CarloUser/Mobile-Mapping-Backpack/opencv/calib_images/img_0.png

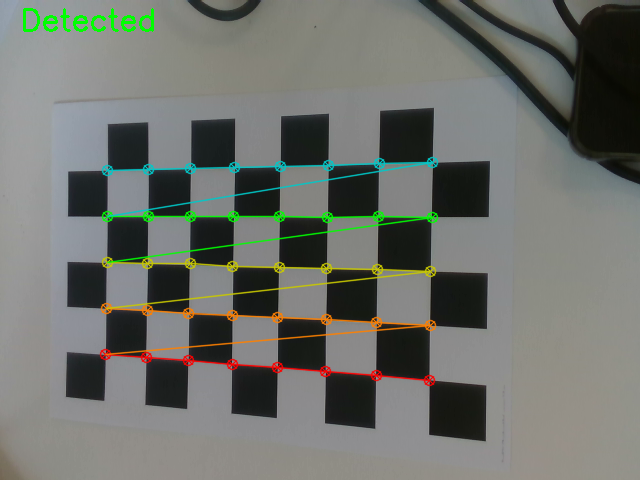
opencv/calib_images/img_0.png
