CarloUser/Mobile-Mapping-Backpack/opencv/calib_images/img_1.png

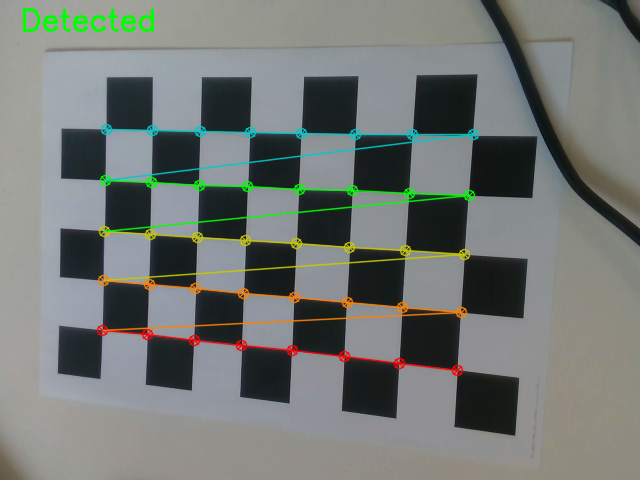
opencv/calib_images/img_1.png
