CarloUser/Mobile-Mapping-Backpack/opencv/calib_images/img_2.png

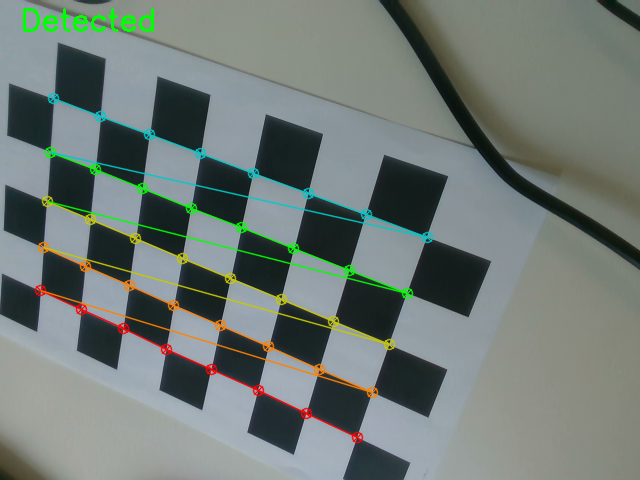
opencv/calib_images/img_2.png
