CarloUser/Mobile-Mapping-Backpack/opencv/calib_images/img_3.png

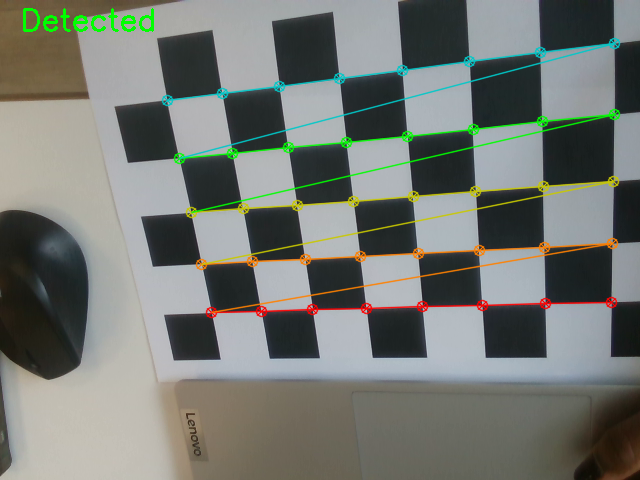
opencv/calib_images/img_3.png
