CarloUser/Mobile-Mapping-Backpack/opencv/calib_images/img_4.png

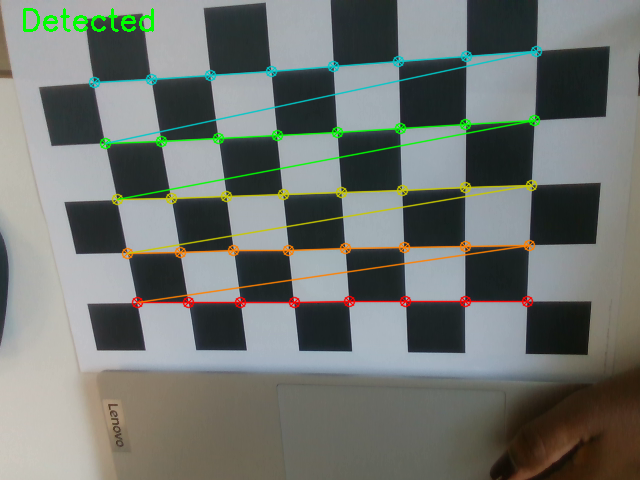
opencv/calib_images/img_4.png
