CarloUser/Mobile-Mapping-Backpack/opencv/calib_images/img_5.png

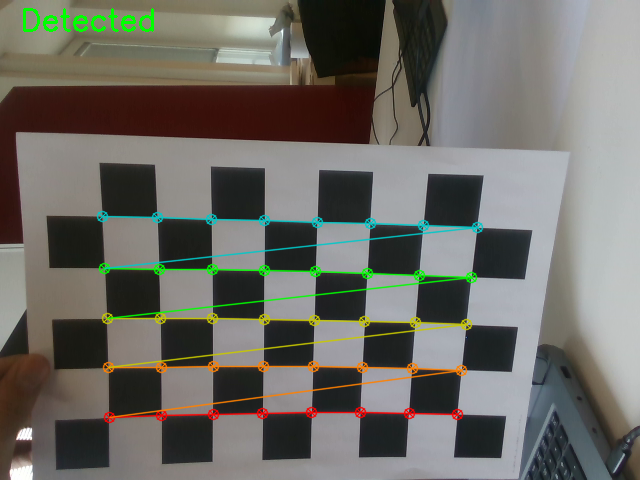
opencv/calib_images/img_5.png
