CarloUser/Mobile-Mapping-Backpack/opencv/calib_images/img_6.png

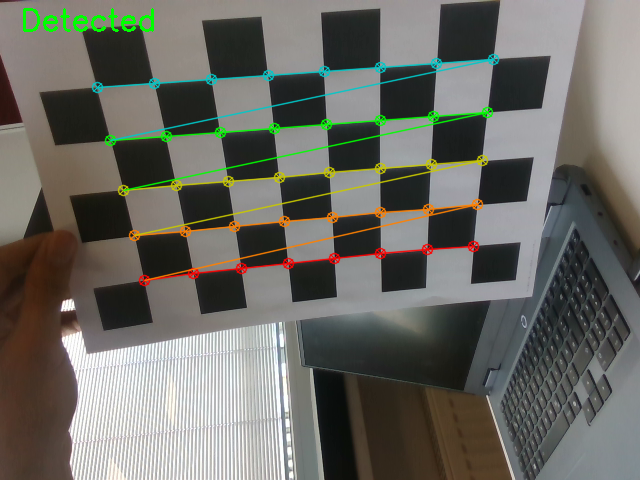
opencv/calib_images/img_6.png
