CarloUser/Mobile-Mapping-Backpack/opencv/calib_images/img_7.png

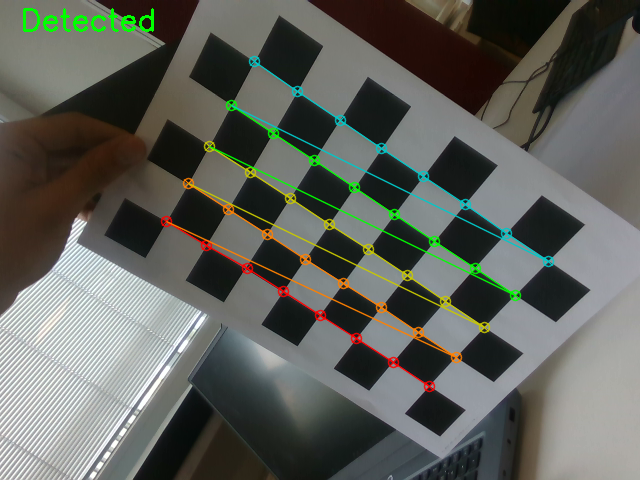
opencv/calib_images/img_7.png
