CarloUser/Mobile-Mapping-Backpack/opencv/calib_images/img_8.png

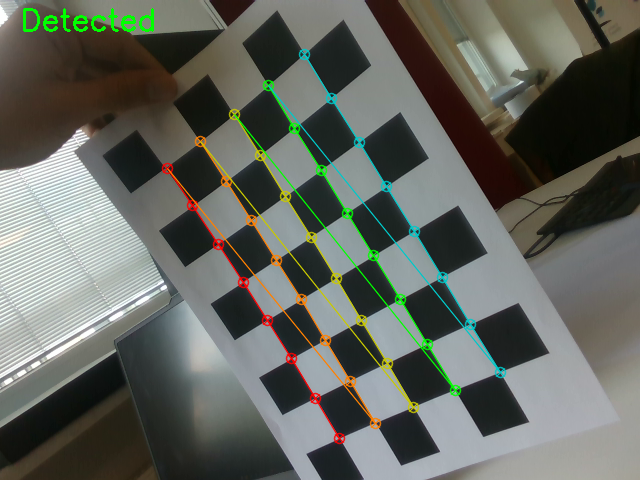
opencv/calib_images/img_8.png
