CarloUser/Mobile-Mapping-Backpack/opencv/calib_images/img_9.png

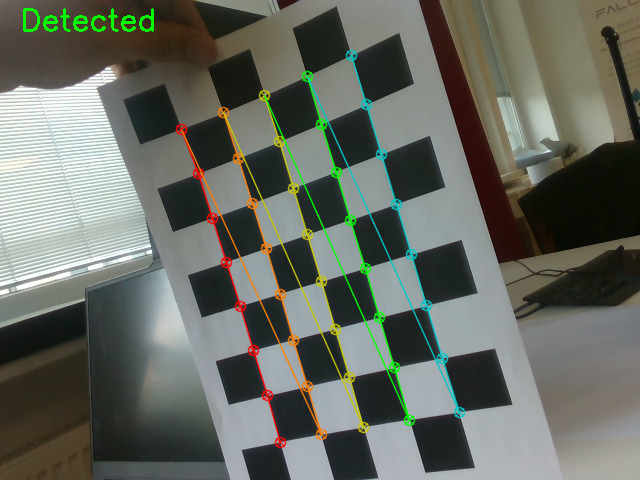
opencv/calib_images/img_9.png
