CarloUser/Mobile-Mapping-Backpack/opencv/calib_images/img_10.png

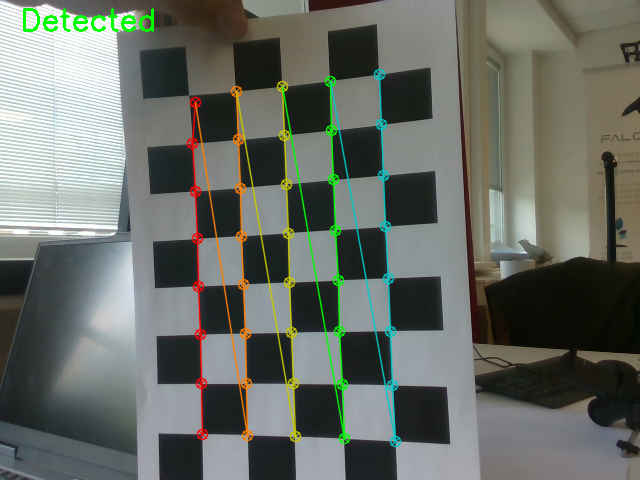
opencv/calib_images/img_10.png
