CarloUser/Mobile-Mapping-Backpack/opencv/calib_images/img_11.png

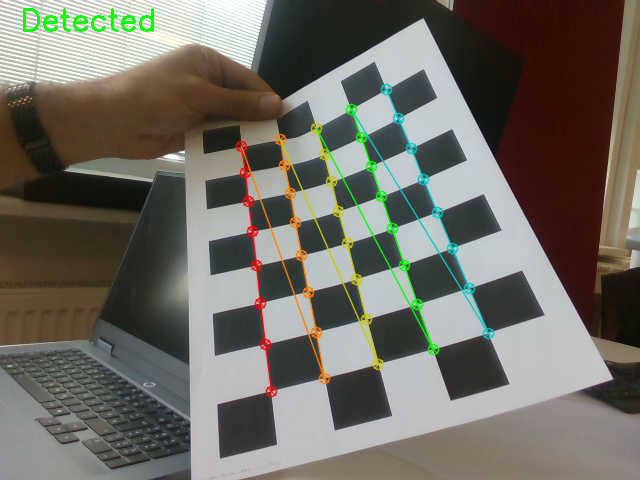
opencv/calib_images/img_11.png
