CarloUser/Mobile-Mapping-Backpack/opencv/calib_images/img_12.png

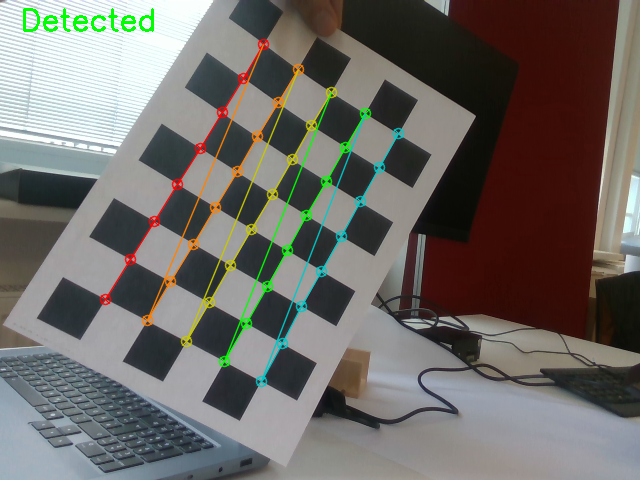
opencv/calib_images/img_12.png
