CarloUser/Mobile-Mapping-Backpack/opencv/calib_images/img_13.png

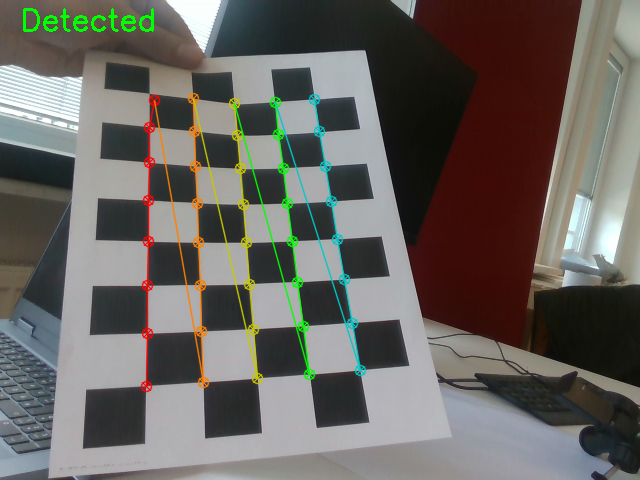
opencv/calib_images/img_13.png
