CarloUser/Mobile-Mapping-Backpack/opencv/calib_images/img_14.png

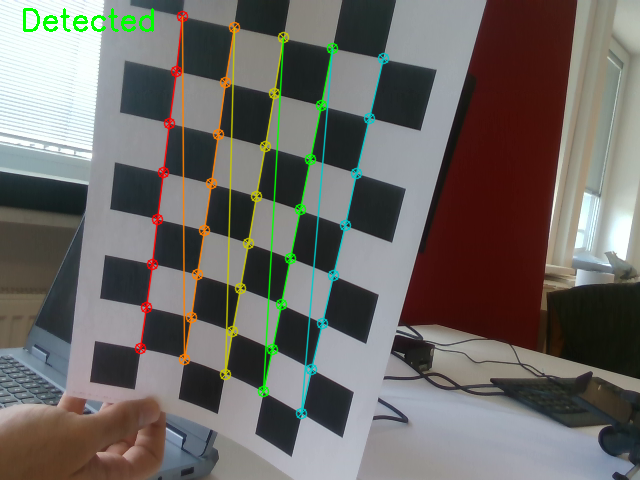
opencv/calib_images/img_14.png
