CarloUser/Mobile-Mapping-Backpack/opencv/calib_images/img_15.png

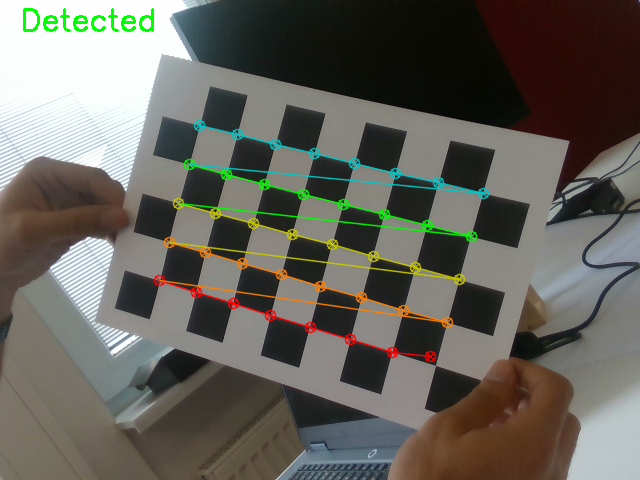
opencv/calib_images/img_15.png
