CarloUser/Mobile-Mapping-Backpack/opencv/calib_images/img_16.png

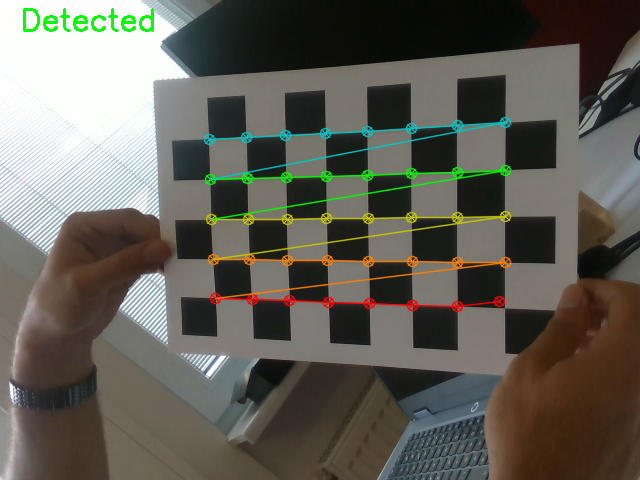
opencv/calib_images/img_16.png
