CarloUser/Mobile-Mapping-Backpack/opencv/calib_images/img_17.png

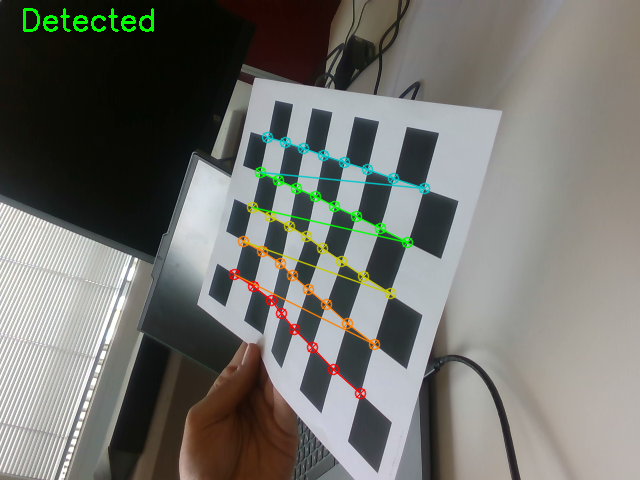
opencv/calib_images/img_17.png
