CarloUser/Mobile-Mapping-Backpack/opencv/calib_images/img_18.png

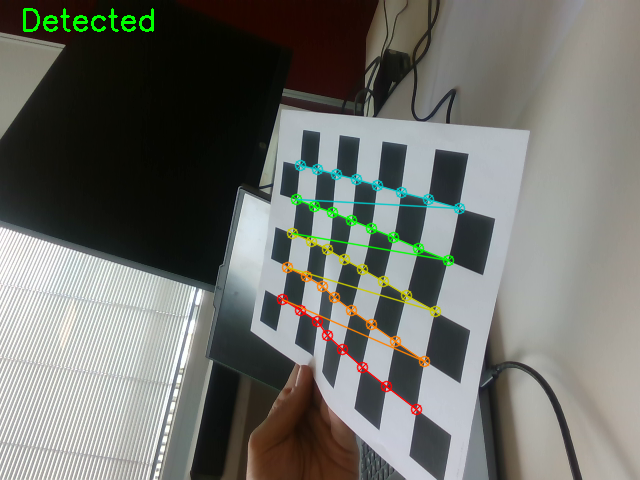
opencv/calib_images/img_18.png
