CarloUser/Mobile-Mapping-Backpack/opencv/calib_images/img_19.png

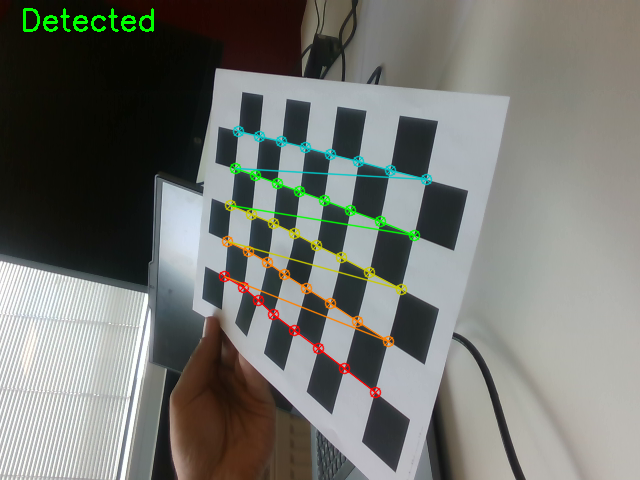
opencv/calib_images/img_19.png
