CarloUser/Mobile-Mapping-Backpack/opencv/calib_images/img_20.png

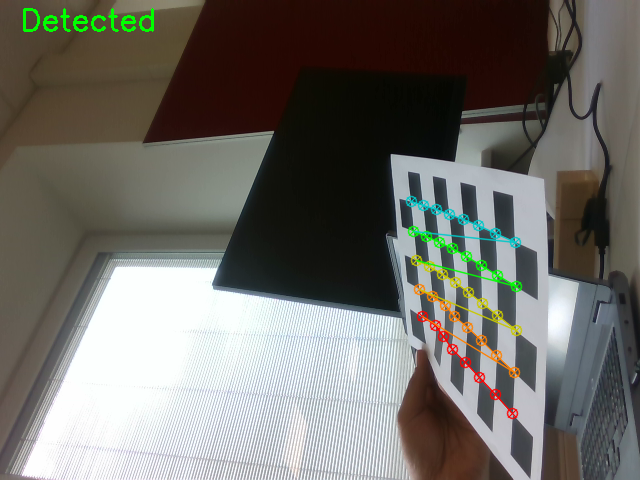
opencv/calib_images/img_20.png
