CarloUser/Mobile-Mapping-Backpack/opencv/calib_images/img_21.png

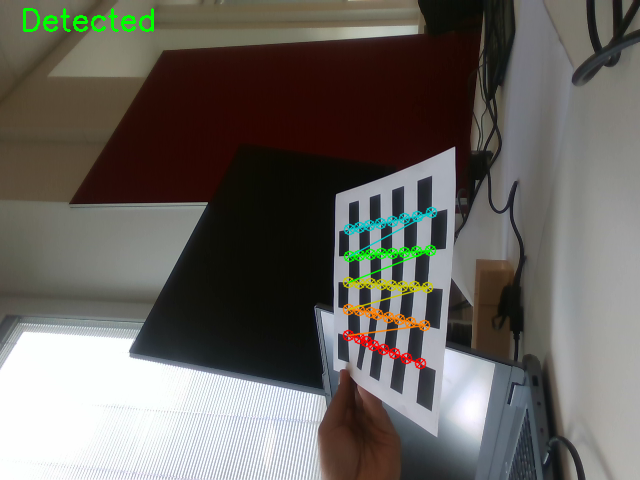
opencv/calib_images/img_21.png
