CarloUser/Mobile-Mapping-Backpack/opencv/calib_images/img_22.png

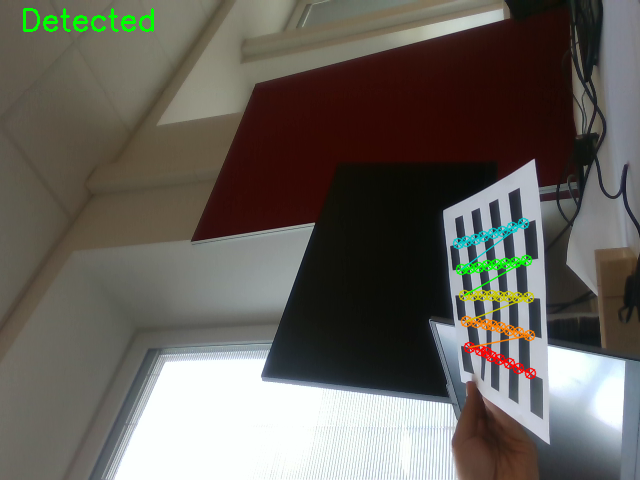
opencv/calib_images/img_22.png
