CarloUser/Mobile-Mapping-Backpack/opencv/calib_images/img_29.png

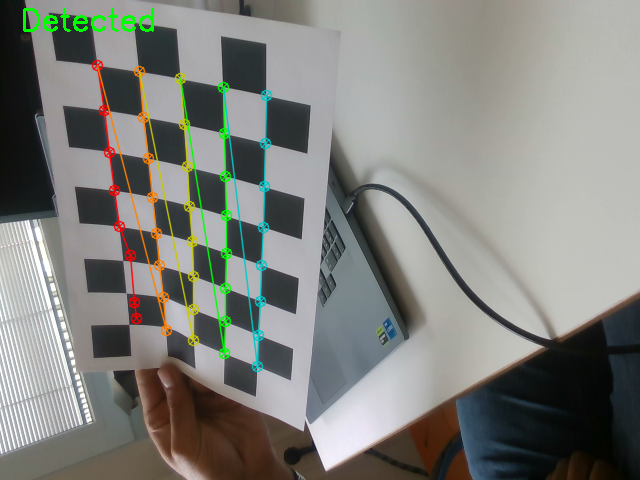
opencv/calib_images/img_29.png
