CarloUser/Mobile-Mapping-Backpack/opencv/calib_images/img_30.png

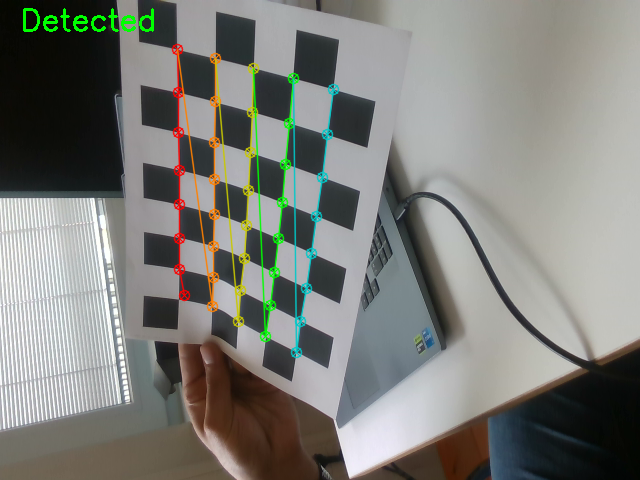
opencv/calib_images/img_30.png
