CarloUser/Mobile-Mapping-Backpack/opencv/calib_images/img_31.png

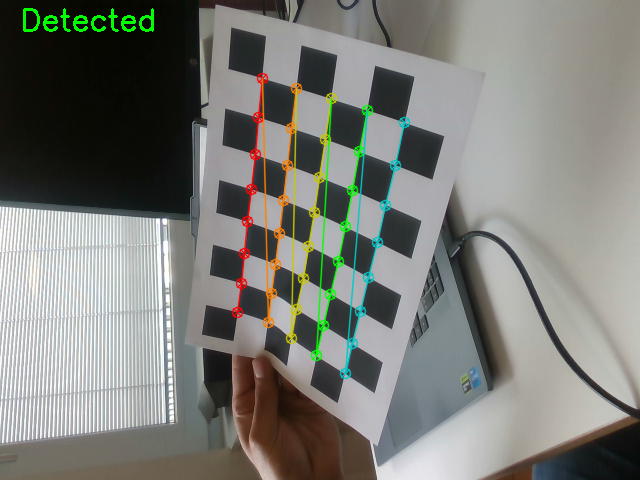
opencv/calib_images/img_31.png
