CarloUser/Mobile-Mapping-Backpack/cad/Sources/Grips/Heavy-Duty Slingshot Rifle.SLDASM

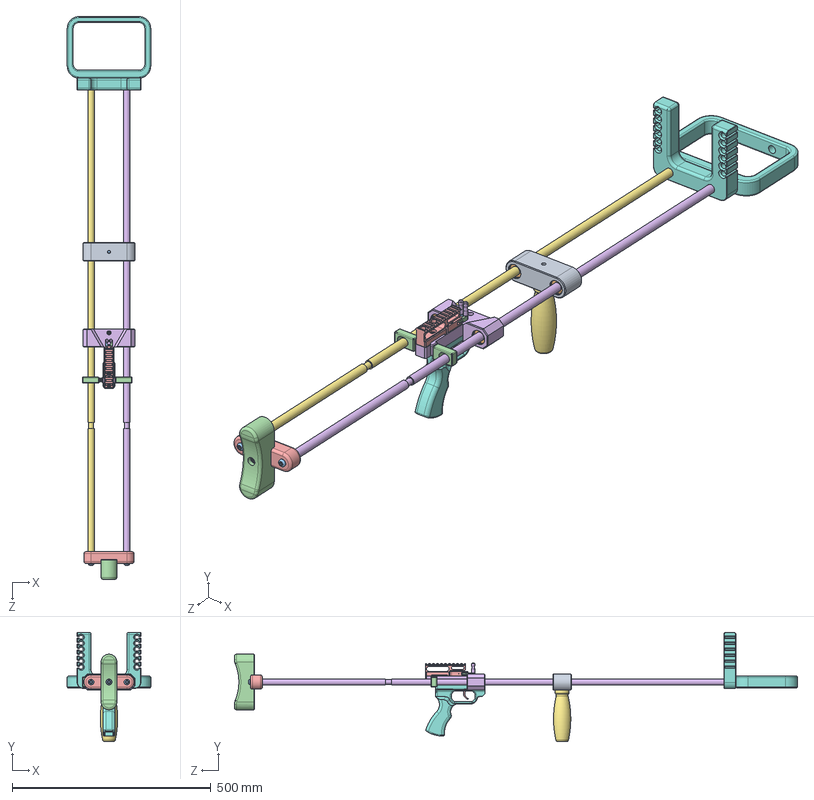
[picture p29: CAD file, 2026-05-12]
cad/Sources/Grips/Heavy-Duty Slingshot Rifle.SLDASM
210.0 x 275.0 x 1415.0 mm
Heavy-duty Slingshot Part-1
Heavy-duty Slingshot Part-2
Heavy-duty Slingshot Part-3
Heavy-duty Slingshot Part-4
Heavy-duty Slingshot Part-5
Heavy-duty Slingshot Part-6 x 6
LM16UU Libear Bearing x 4
Heavy-duty Slingshot Part-8
Heavy-duty Slingshot Part-9
Heavy-duty Slingshot Part-10
Heavy-duty Slingshot Part-11
Slingshot Rifle Part-13
Slingshot Rifle Part-23
Slingshot Rifle Part-24
Slingshot Rifle Part-18 x 2
Slingshot Rifle Part-20 x 2
Slingshot Rifle Part-30
Slingshot Rifle Part-21
Slingshot Rifle Part-19 x 2
Slingshot Rifle Part-26
Slingshot Rifle Part-27
Slingshot Rifle Part-28
Slingshot Rifle Part-29
Slingshot Rifle Part-14 x 4
Slingshot Rifle Part-36
Slingshot Rifle Part-37 x 2
Slingshot Rifle Part-10 x 4
Slingshot Rifle Part-12
Heavy-duty Slingshot Part-12 x 2
Heavy-duty Slingshot Part-13
Slingshot Rifle Part-15 x 2
Heavy-duty Slingshot Part-14
