CarloUser/Mobile-Mapping-Backpack/cad/Sources/Grips/Trigger-Asy.SLDASM

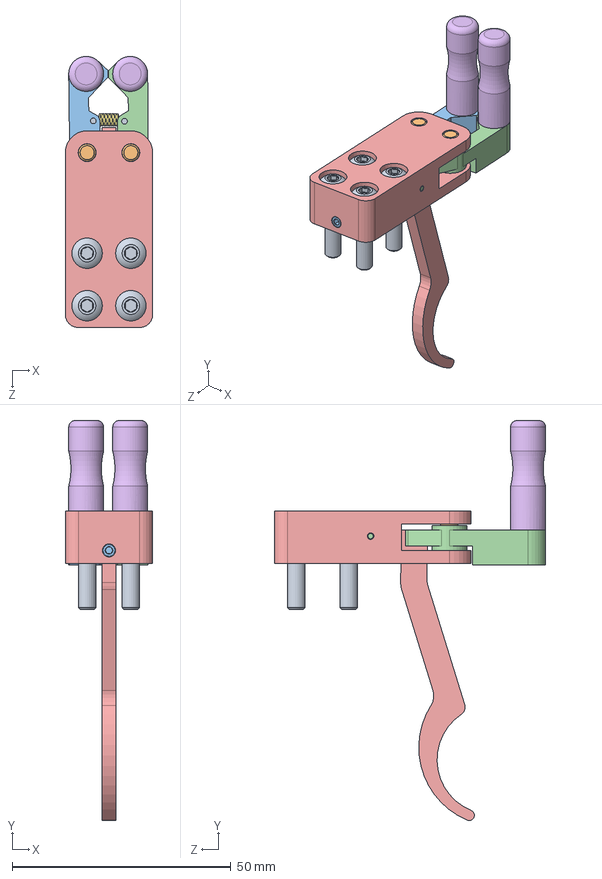
[picture p31: CAD file, 2026-05-12]
cad/Sources/Grips/Trigger-Asy.SLDASM
20.0 x 91.5 x 62.0 mm
Slingshot Rifle Part-13
Slingshot Rifle Part-23
Slingshot Rifle Part-24
Slingshot Rifle Part-18 x 2
Slingshot Rifle Part-20 x 2
Slingshot Rifle Part-30
Slingshot Rifle Part-21
Slingshot Rifle Part-19 x 2
Slingshot Rifle Part-26
Slingshot Rifle Part-27
Slingshot Rifle Part-28
Slingshot Rifle Part-29
Slingshot Rifle Part-14 x 4
