CarloUser/Mobile-Mapping-Backpack/cad/Handheld/V3_STL/Rail_Bottom_V3.STL

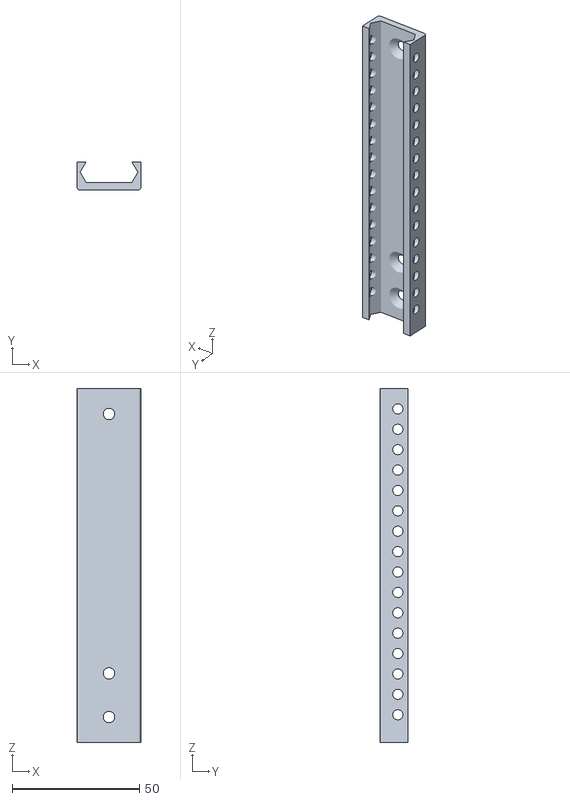
[picture p45: CAD file, 2026-05-12]
cad/Handheld/V3_STL/Rail_Bottom_V3.STL
25.0 x 11.0 x 138.9
