CarloUser/Mobile-Mapping-Backpack/cad/Sources/Blickfeld/Cube 1-Mounting.stp

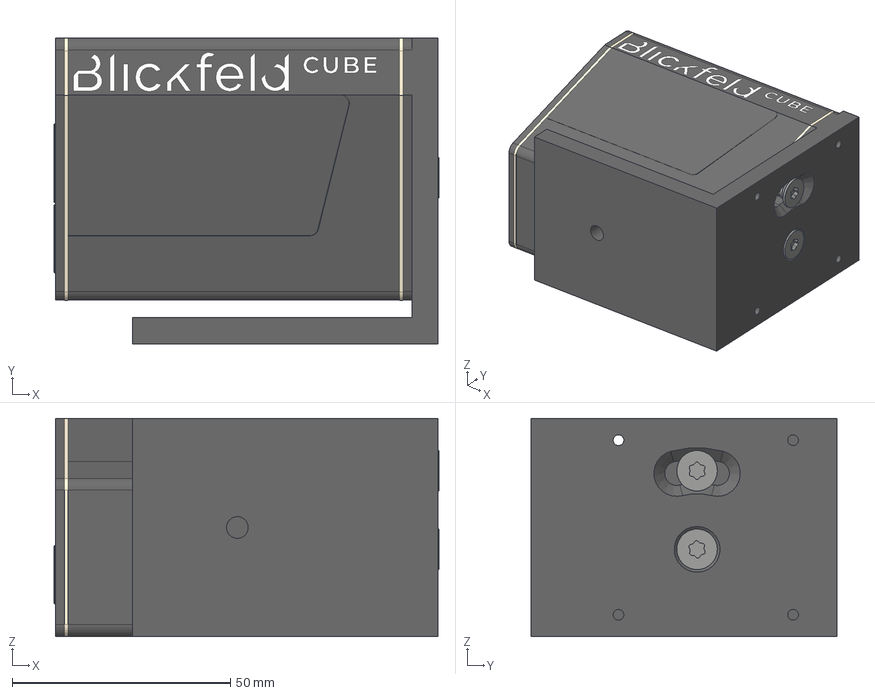
[picture p46: CAD file, 2026-05-12]
cad/Sources/Blickfeld/Cube 1-Mounting.stp
88.2 x 70.0 x 50.0 mm
