CarloUser/Mobile-Mapping-Backpack/cad/Sources/Grips/Slingshot Rifle Part-30.SLDPRT

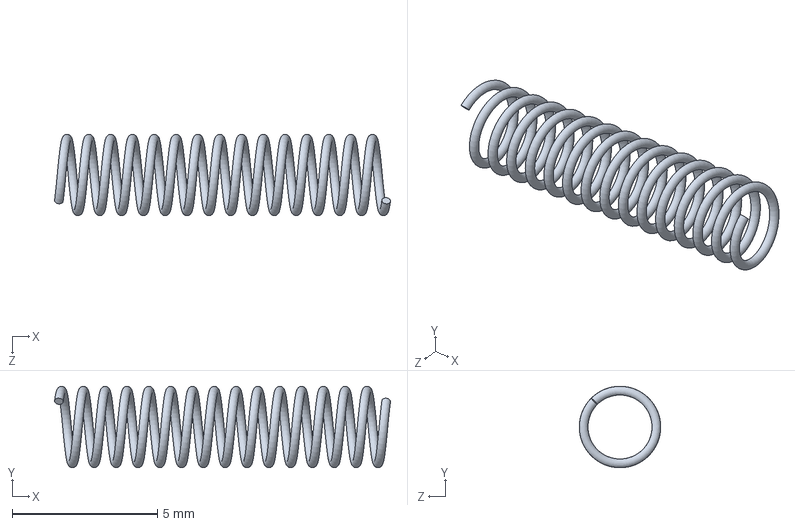
[picture p47: CAD file, 2026-05-12]
cad/Sources/Grips/Slingshot Rifle Part-30.SLDPRT
11.5 x 2.80 x 2.80 mm
