CarloUser/Mobile-Mapping-Backpack/cad/Handheld/V3_STL/Mount_V3.STL

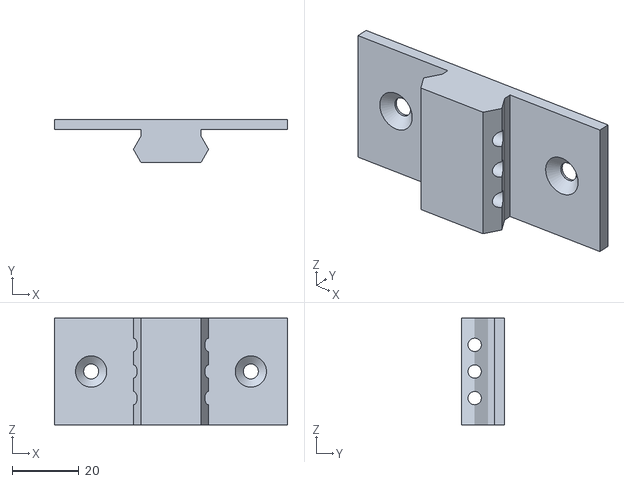
[picture p48: CAD file, 2026-05-12]
cad/Handheld/V3_STL/Mount_V3.STL
70.0 x 13.0 x 32.0
