CarloUser/Mobile-Mapping-Backpack/cad/Handheld/V4/OakLite_Mount.SLDPRT

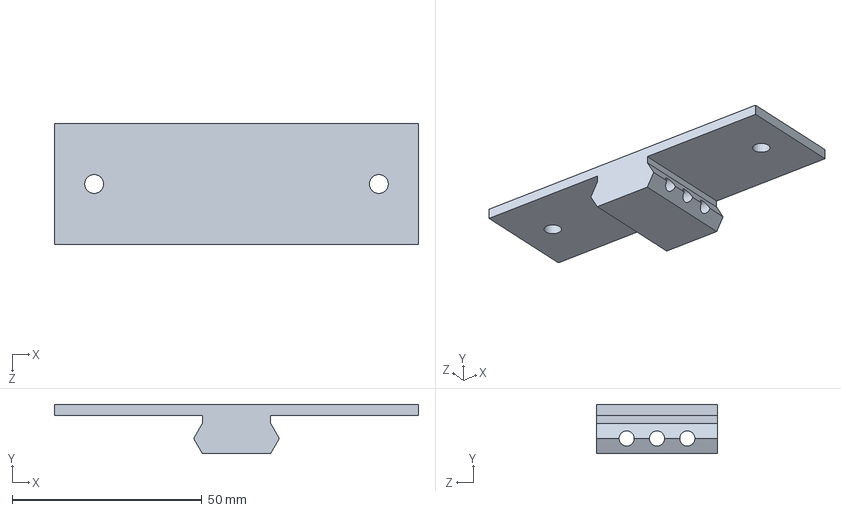
[picture p49: CAD file, 2026-05-12]
cad/Handheld/V4/OakLite_Mount.SLDPRT
96.0 x 13.0 x 32.0 mm
