CarloUser/Mobile-Mapping-Backpack/cad/Sources/Grips/Slingshot Rifle Part-13.SLDPRT

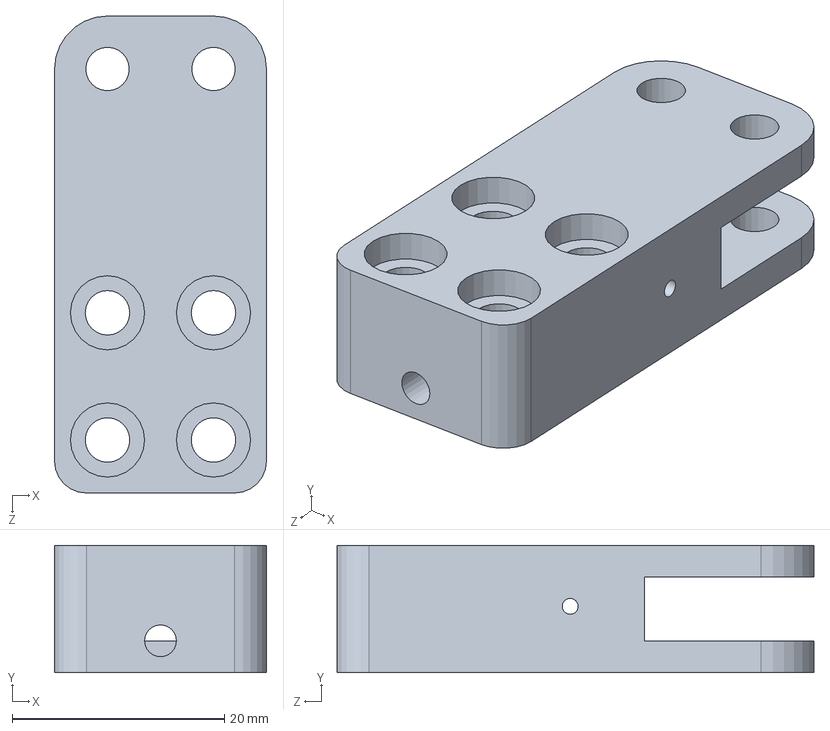
[picture p50: CAD file, 2026-05-12]
cad/Sources/Grips/Slingshot Rifle Part-13.SLDPRT
20.0 x 12.0 x 45.0 mm
