CarloUser/Mobile-Mapping-Backpack/cad/Sources/Grips/Heavy-duty Slingshot Part-6.SLDPRT

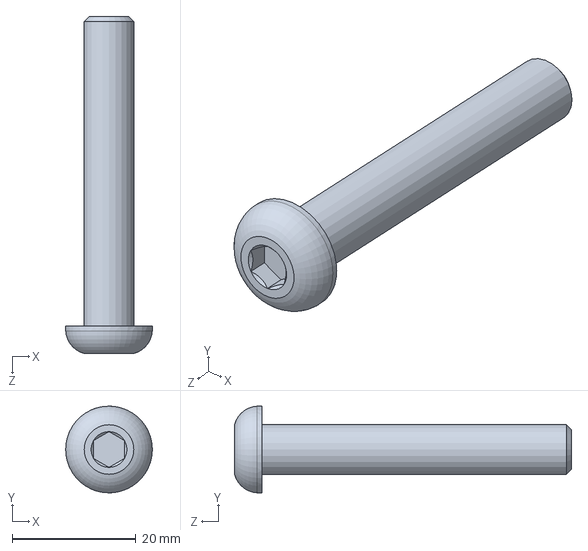
[picture p52: CAD file, 2026-05-12]
cad/Sources/Grips/Heavy-duty Slingshot Part-6.SLDPRT
14.0 x 14.0 x 54.4 mm
