CarloUser/Mobile-Mapping-Backpack/cad/Handheld/V3_STL/CubeMount_V3.STL

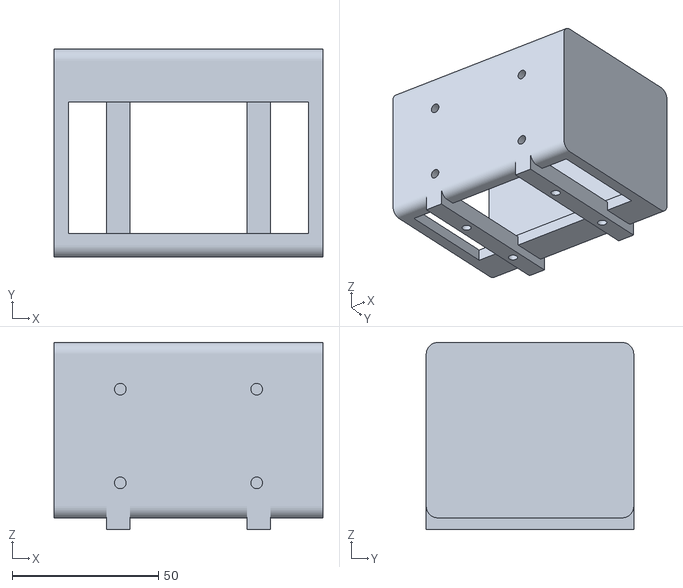
[picture p53: CAD file, 2026-05-12]
cad/Handheld/V3_STL/CubeMount_V3.STL
92.0 x 71.0 x 64.0
