CarloUser/Mobile-Mapping-Backpack/cad/Sources/Grips/Slingshot Rifle Part-29.SLDPRT

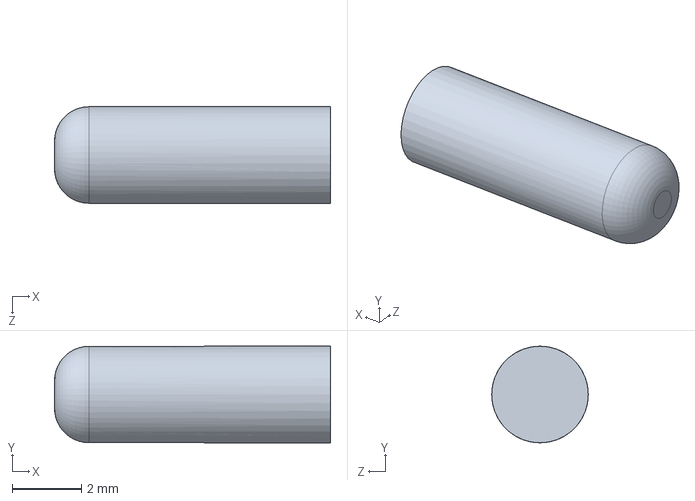
[picture p54: CAD file, 2026-05-12]
cad/Sources/Grips/Slingshot Rifle Part-29.SLDPRT
8.00 x 2.80 x 2.80 mm
