CarloUser/Mobile-Mapping-Backpack/cad/Handheld/V3_STL/Rail_Top_V3.STL

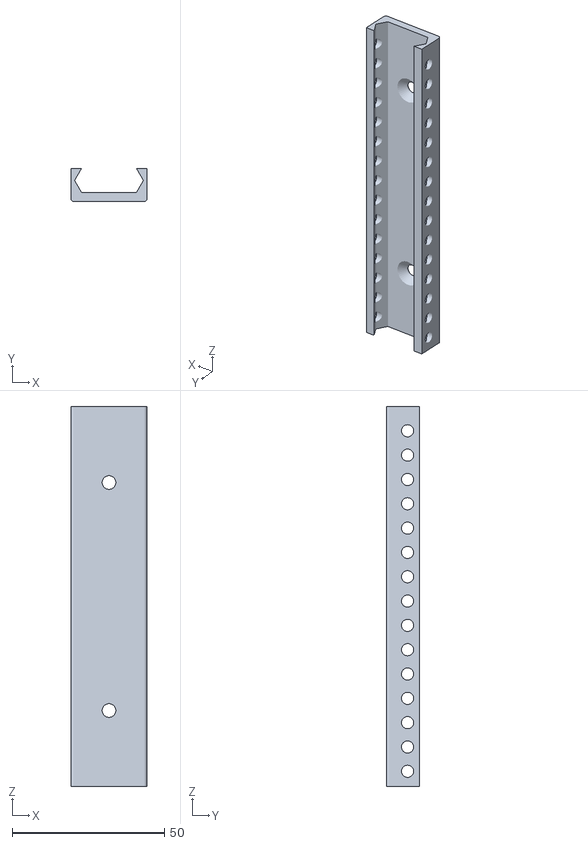
[picture p55: CAD file, 2026-05-12]
cad/Handheld/V3_STL/Rail_Top_V3.STL
25.0 x 11.0 x 125.0
