CarloUser/Mobile-Mapping-Backpack/cad/Sources/Grips/Heavy-duty Slingshot Part-9.SLDPRT

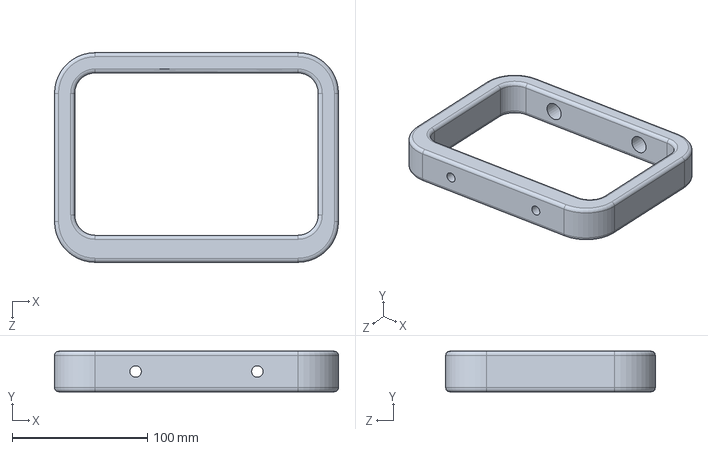
[picture p56: CAD file, 2026-05-12]
cad/Sources/Grips/Heavy-duty Slingshot Part-9.SLDPRT
210.0 x 30.0 x 155.0 mm
