CarloUser/Mobile-Mapping-Backpack/cad/Handheld/V3_STL/Camera_Adapter.STL

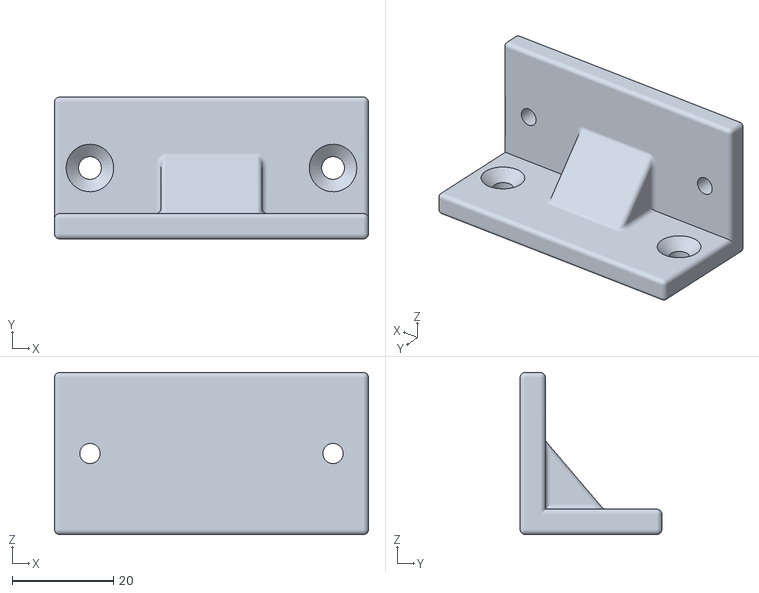
[picture p57: CAD file, 2026-05-12]
cad/Handheld/V3_STL/Camera_Adapter.STL
62.0 x 28.0 x 32.0
