CarloUser/Mobile-Mapping-Backpack/cad/Sources/Grips/Heavy-duty Slingshot Part-12.SLDPRT

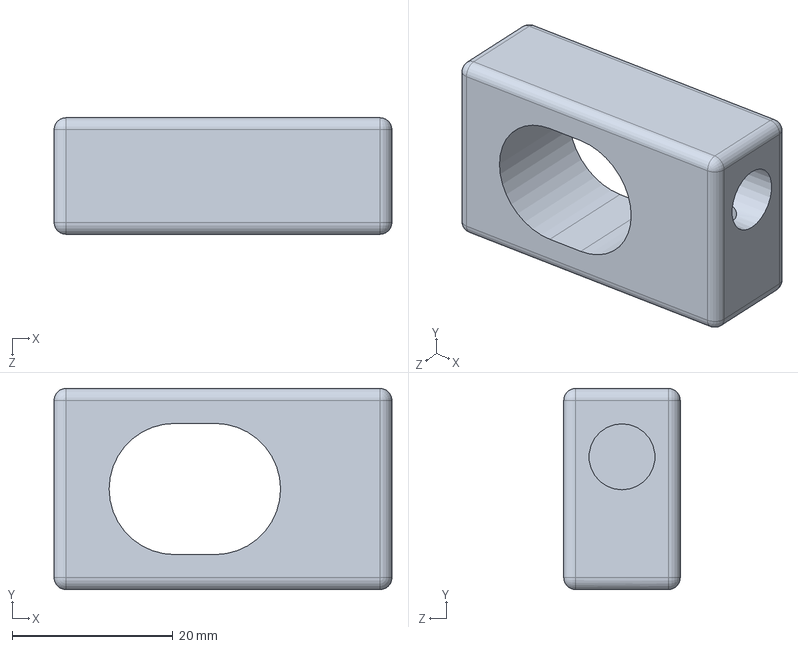
[picture p58: CAD file, 2026-05-12]
cad/Sources/Grips/Heavy-duty Slingshot Part-12.SLDPRT
42.0 x 25.0 x 14.5 mm
