CarloUser/Mobile-Mapping-Backpack/cad/Sources/Grips/Slingshot Rifle Part-10.SLDPRT

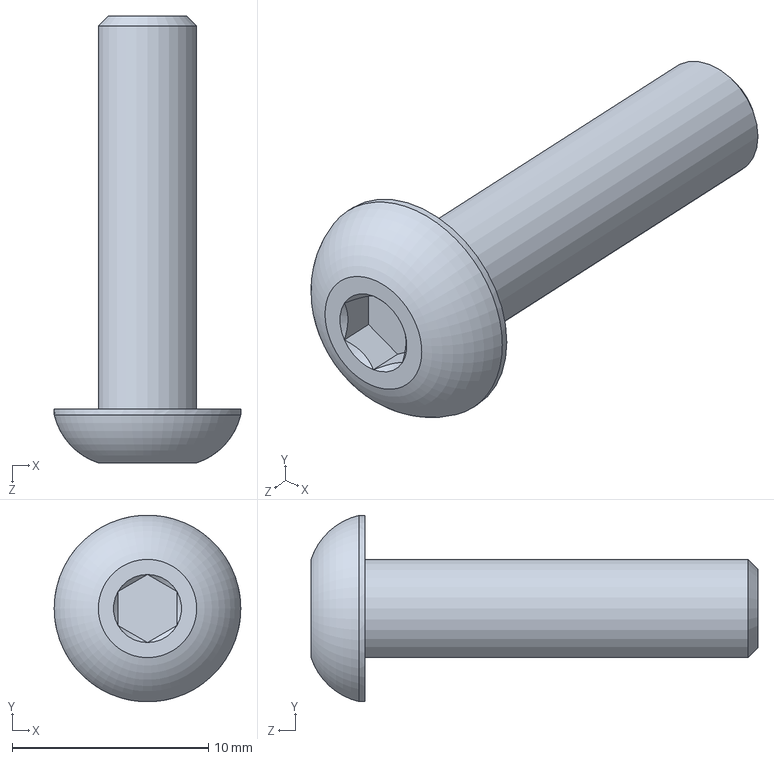
[picture p59: CAD file, 2026-05-12]
cad/Sources/Grips/Slingshot Rifle Part-10.SLDPRT
9.50 x 9.48 x 22.8 mm
