CarloUser/Mobile-Mapping-Backpack/cad/Sources/Grips/Slingshot Rifle Part-14.SLDPRT

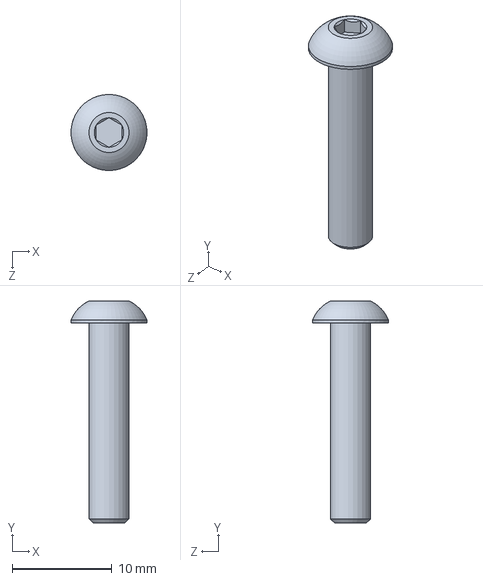
[picture p60: CAD file, 2026-05-12]
cad/Sources/Grips/Slingshot Rifle Part-14.SLDPRT
7.60 x 22.2 x 7.60 mm
