CarloUser/Mobile-Mapping-Backpack/cad/Sources/Grips/Slingshot Rifle Part-18.SLDPRT

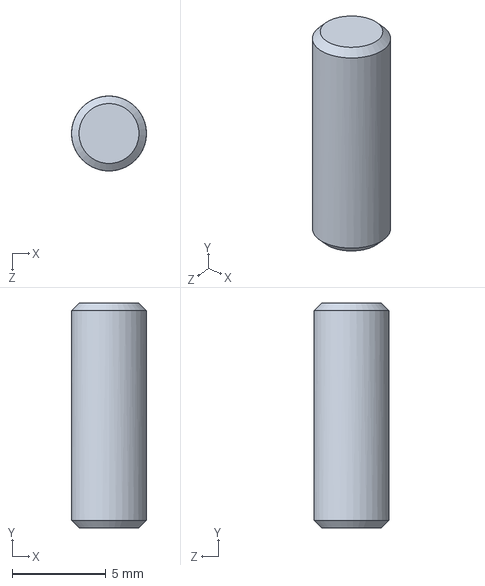
[picture p61: CAD file, 2026-05-12]
cad/Sources/Grips/Slingshot Rifle Part-18.SLDPRT
4.00 x 12.0 x 4.00 mm
