CarloUser/Mobile-Mapping-Backpack/cad/Sources/Grips/Slingshot Rifle Part-26.SLDPRT

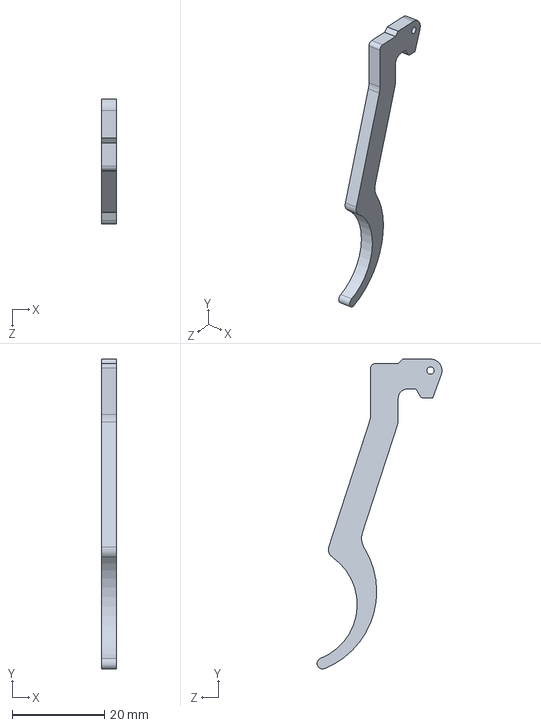
[picture p62: CAD file, 2026-05-12]
cad/Sources/Grips/Slingshot Rifle Part-26.SLDPRT
3.30 x 67.2 x 27.1 mm
