CarloUser/Mobile-Mapping-Backpack/cad/Sources/Grips/Heavy-duty Slingshot Part-2.SLDPRT

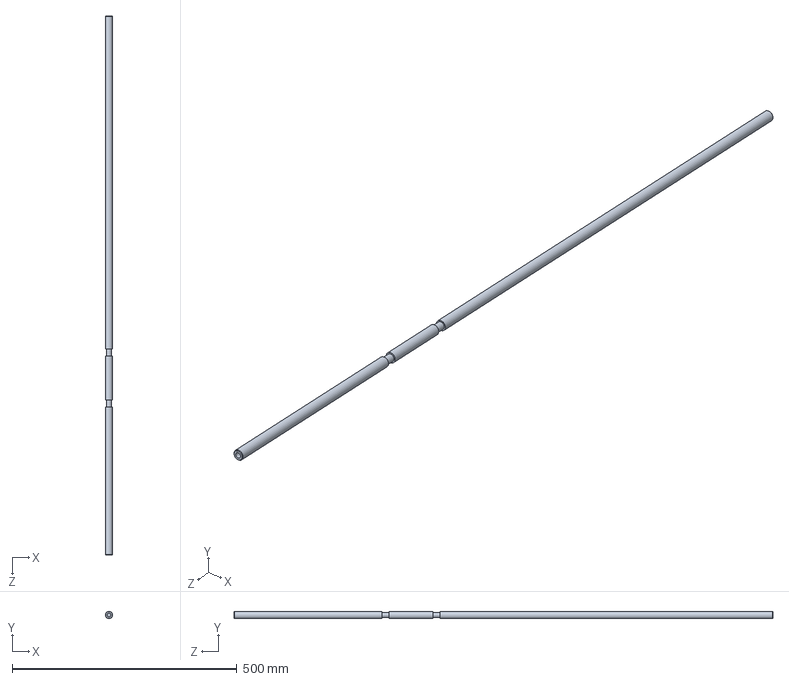
[picture p63: CAD file, 2026-05-12]
cad/Sources/Grips/Heavy-duty Slingshot Part-2.SLDPRT
16.0 x 16.0 x 1200.0 mm
