CarloUser/Mobile-Mapping-Backpack/cad/Sources/Grips/Heavy-duty Slingshot Part-5.SLDPRT

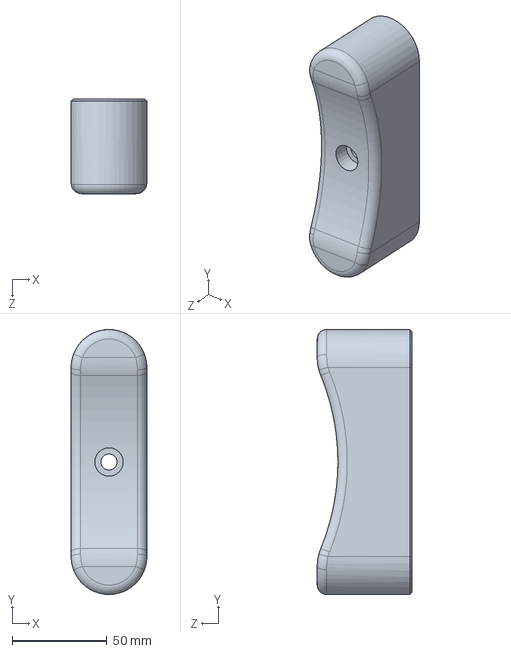
[picture p64: CAD file, 2026-05-12]
cad/Sources/Grips/Heavy-duty Slingshot Part-5.SLDPRT
40.0 x 140.0 x 50.0 mm
