CarloUser/Mobile-Mapping-Backpack/cad/Sources/Grips/Slingshot Rifle Part-21.SLDPRT

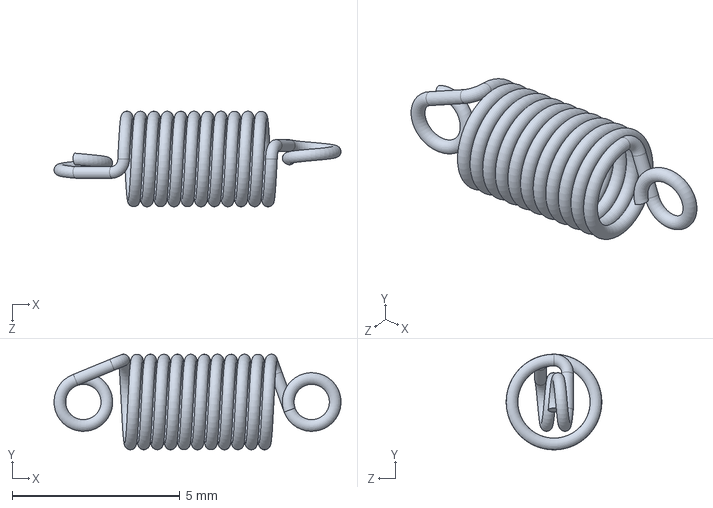
[picture p65: CAD file, 2026-05-12]
cad/Sources/Grips/Slingshot Rifle Part-21.SLDPRT
8.55 x 2.85 x 2.85 mm
