CarloUser/Mobile-Mapping-Backpack/cad/Sources/Grips/Heavy-duty Slingshot Part-8.SLDPRT

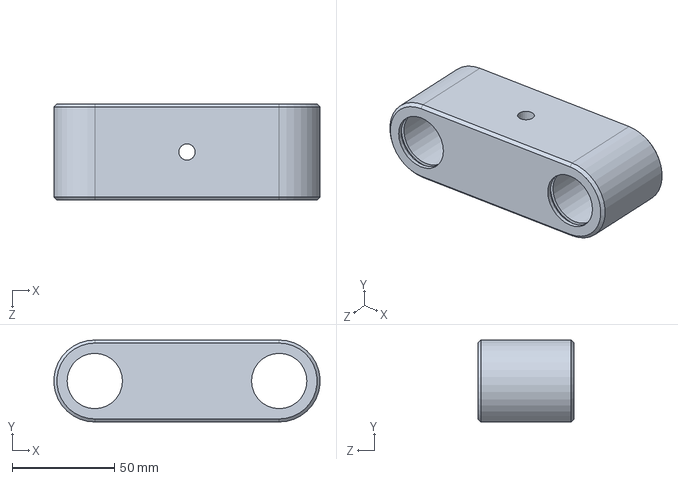
[picture p66: CAD file, 2026-05-12]
cad/Sources/Grips/Heavy-duty Slingshot Part-8.SLDPRT
129.8 x 40.0 x 47.0 mm
