CarloUser/Mobile-Mapping-Backpack/cad/Sources/Grips/Slingshot Rifle Part-36.SLDPRT

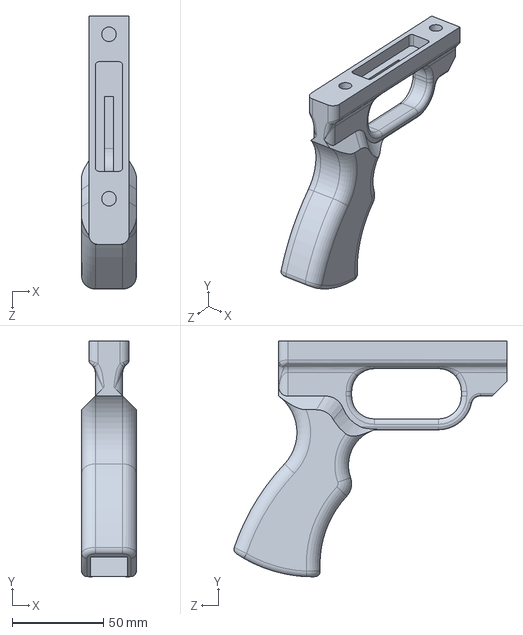
[picture p67: CAD file, 2026-05-12]
cad/Sources/Grips/Slingshot Rifle Part-36.SLDPRT
30.0 x 128.9 x 149.4 mm
