CarloUser/Mobile-Mapping-Backpack/cad/Sources/Grips/Slingshot Rifle Part-24.SLDPRT

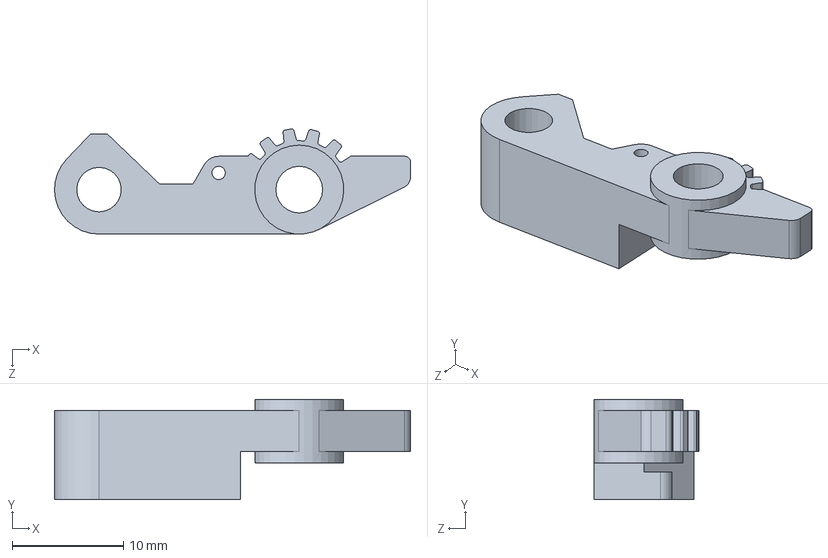
[picture p68: CAD file, 2026-05-12]
cad/Sources/Grips/Slingshot Rifle Part-24.SLDPRT
32.0 x 9.00 x 9.46 mm
