CarloUser/Mobile-Mapping-Backpack/cad/Sources/Grips/Heavy-duty Slingshot Part-1.SLDPRT

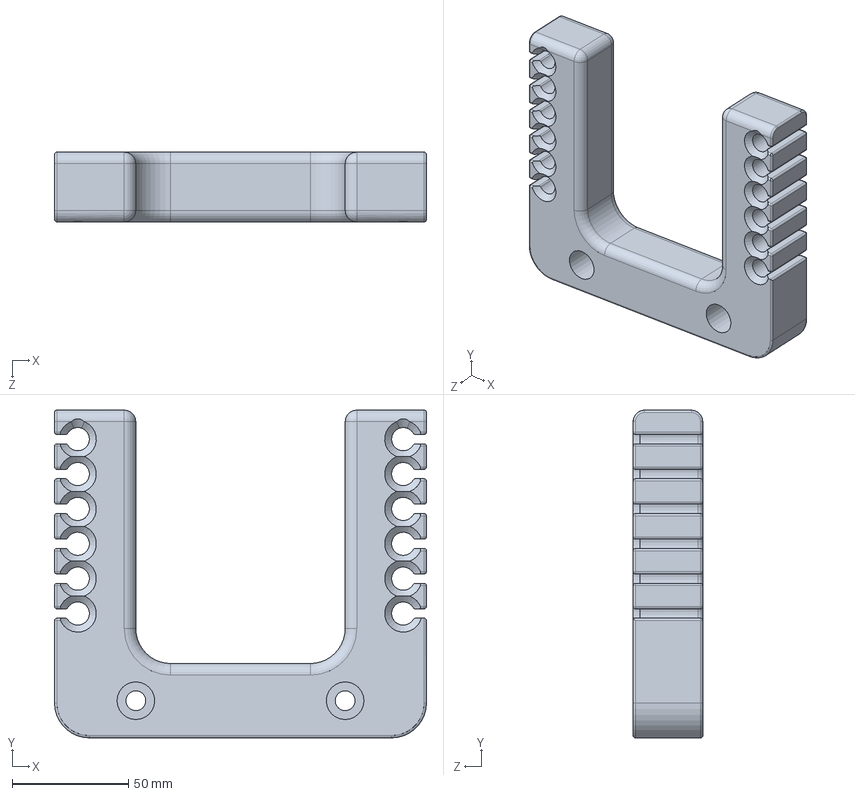
[picture p69: CAD file, 2026-05-12]
cad/Sources/Grips/Heavy-duty Slingshot Part-1.SLDPRT
160.0 x 141.0 x 30.0 mm
