CarloUser/Mobile-Mapping-Backpack/cad/Sources/Grips/Slingshot Rifle Part-19.SLDPRT

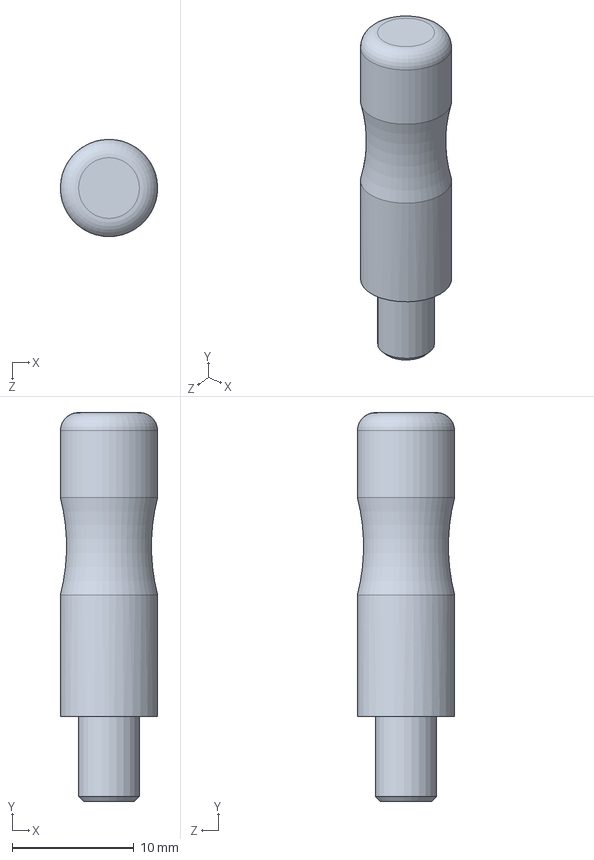
[picture p70: CAD file, 2026-05-12]
cad/Sources/Grips/Slingshot Rifle Part-19.SLDPRT
8.00 x 32.0 x 8.00 mm
