CarloUser/Mobile-Mapping-Backpack/cad/Sources/Grips/Heavy-duty Slingshot Part-14.SLDPRT

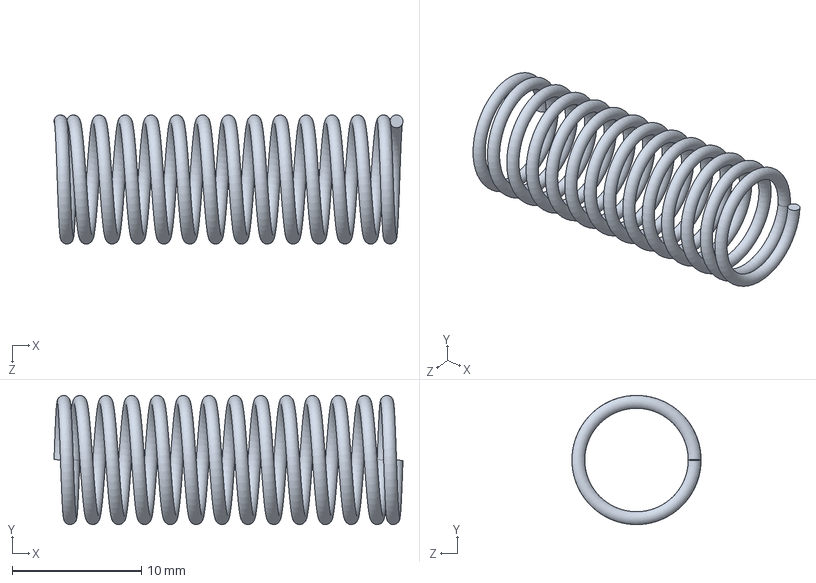
[picture p71: CAD file, 2026-05-12]
cad/Sources/Grips/Heavy-duty Slingshot Part-14.SLDPRT
27.0 x 10.00 x 10.00 mm
