CarloUser/Mobile-Mapping-Backpack/cad/Sources/Grips/Slingshot Rifle Part-28.SLDPRT

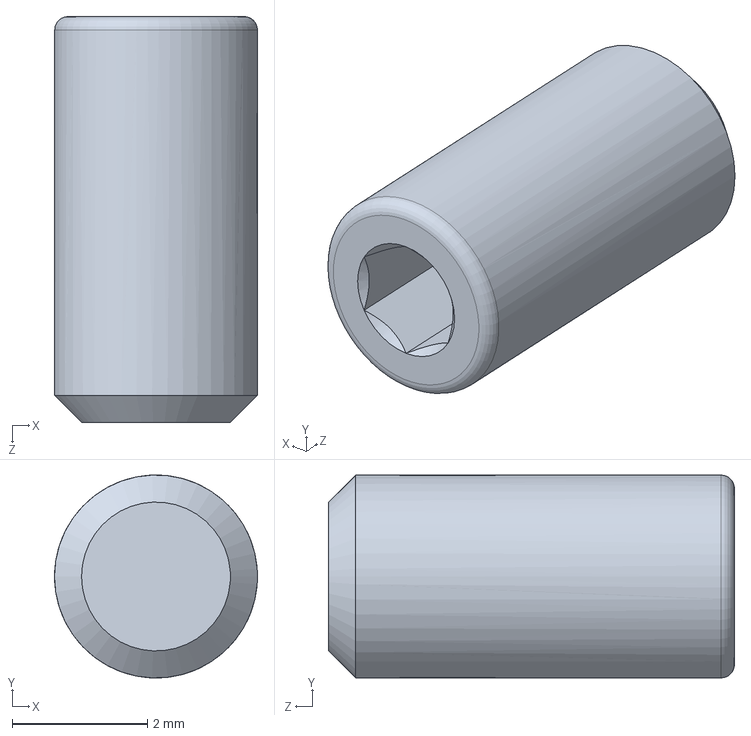
[picture p72: CAD file, 2026-05-12]
cad/Sources/Grips/Slingshot Rifle Part-28.SLDPRT
3.00 x 3.00 x 6.00 mm
