CarloUser/Mobile-Mapping-Backpack/cad/Sources/Grips/Slingshot Rifle Part-37.SLDPRT

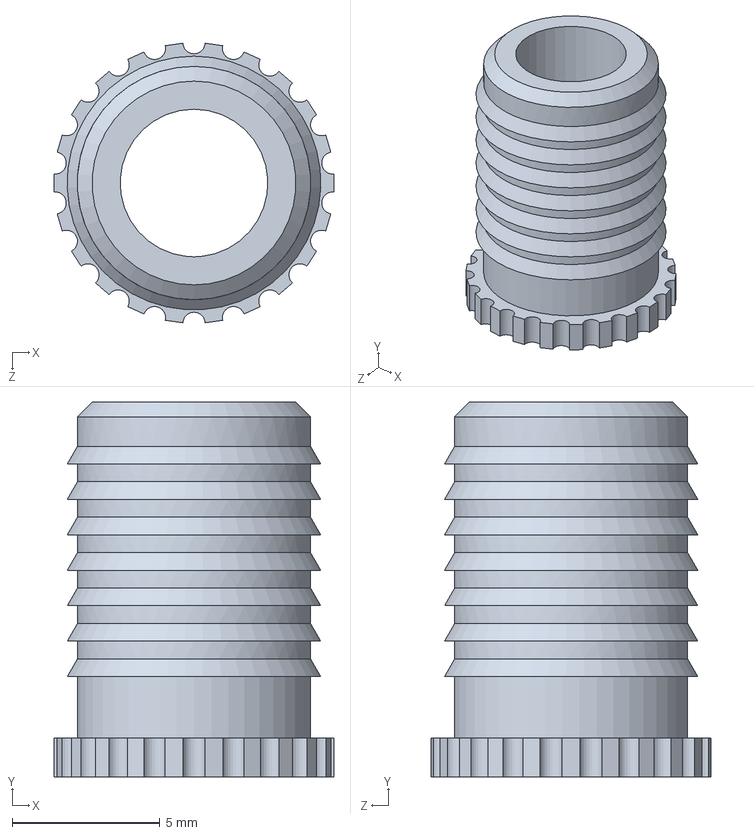
[picture p73: CAD file, 2026-05-12]
cad/Sources/Grips/Slingshot Rifle Part-37.SLDPRT
9.48 x 12.7 x 9.47 mm
