CarloUser/Mobile-Mapping-Backpack/cad/Sources/Grips/Heavy-duty Slingshot Part-7.SLDPRT

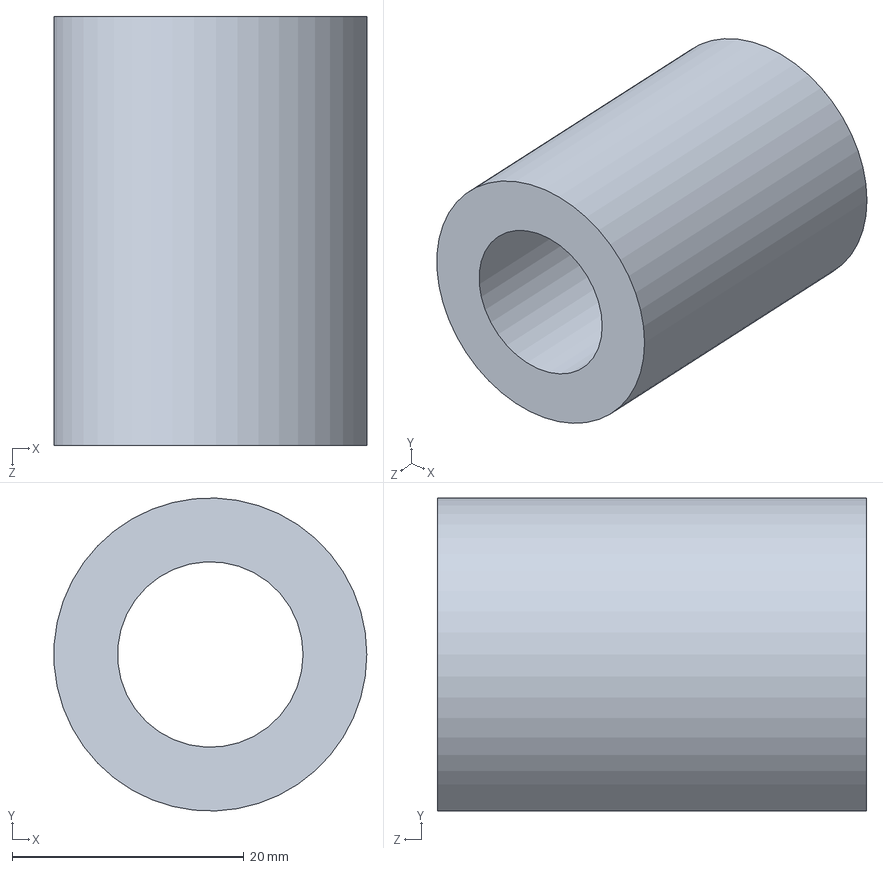
[picture p74: CAD file, 2026-05-12]
cad/Sources/Grips/Heavy-duty Slingshot Part-7.SLDPRT
27.0 x 27.0 x 37.0 mm
