CarloUser/Mobile-Mapping-Backpack/cad/Sources/Grips/Heavy-duty Slingshot Part-4.SLDPRT

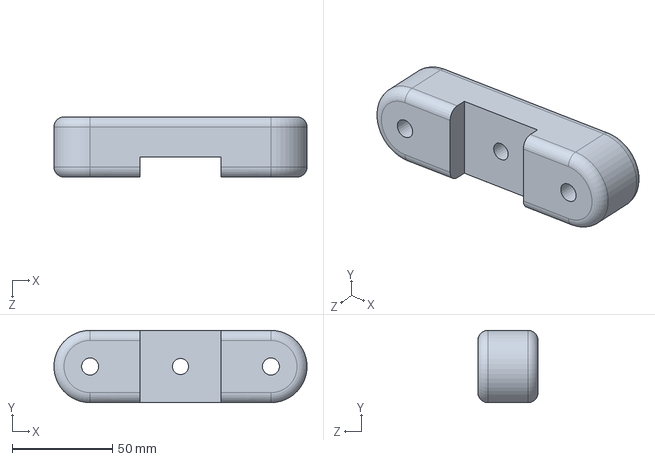
[picture p75: CAD file, 2026-05-12]
cad/Sources/Grips/Heavy-duty Slingshot Part-4.SLDPRT
125.9 x 36.0 x 30.0 mm
