CarloUser/Mobile-Mapping-Backpack/cad/Sources/Grips/Slingshot Rifle Part-27.SLDPRT

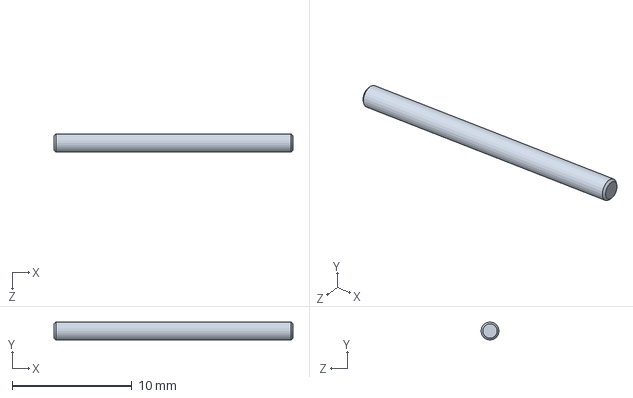
[picture p76: CAD file, 2026-05-12]
cad/Sources/Grips/Slingshot Rifle Part-27.SLDPRT
20.0 x 1.50 x 1.50 mm
