CarloUser/Mobile-Mapping-Backpack/cad/Sources/Grips/Slingshot Rifle Part-15.SLDPRT

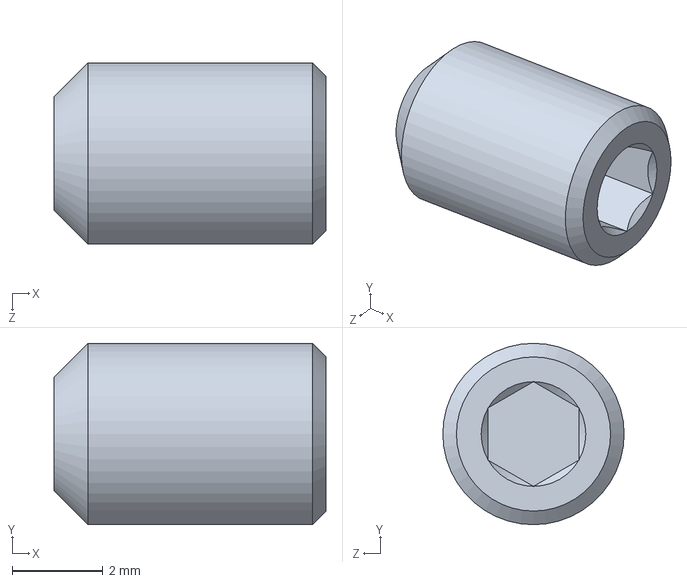
[picture p77: CAD file, 2026-05-12]
cad/Sources/Grips/Slingshot Rifle Part-15.SLDPRT
6.00 x 4.00 x 4.00 mm
