CarloUser/Mobile-Mapping-Backpack/cad/Sources/Grips/Heavy-duty Slingshot Part-10.SLDPRT

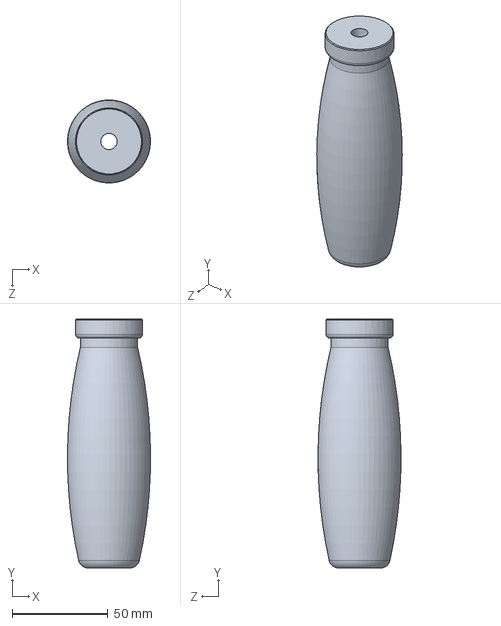
[picture p78: CAD file, 2026-05-12]
cad/Sources/Grips/Heavy-duty Slingshot Part-10.SLDPRT
43.4 x 130.0 x 43.3 mm
