CarloUser/Mobile-Mapping-Backpack/cad/Sources/Grips/Slingshot Rifle Part-12.SLDPRT

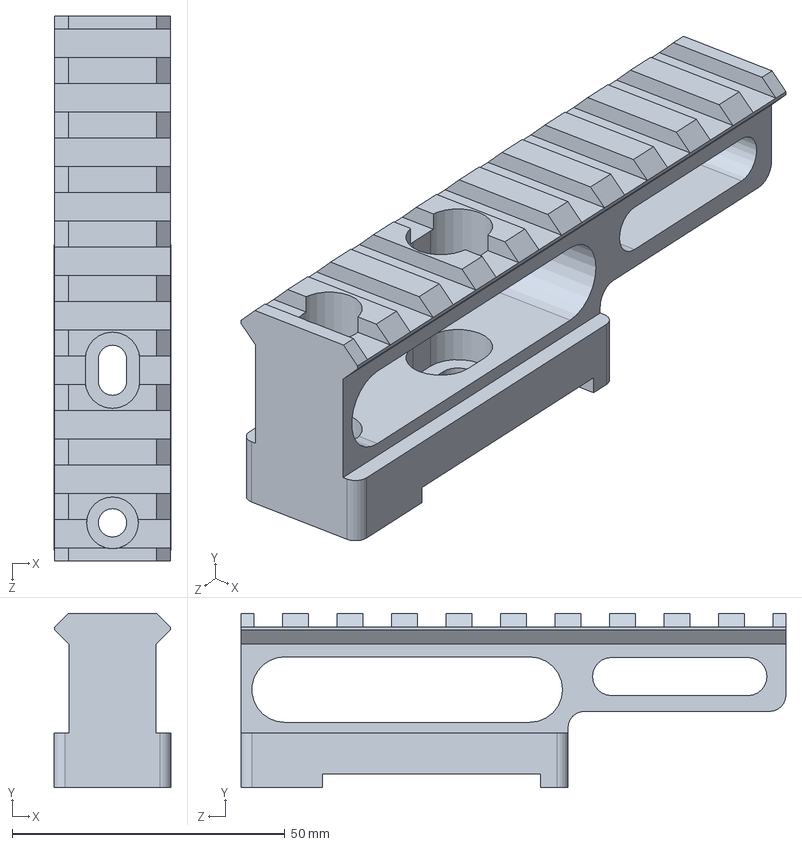
[picture p79: CAD file, 2026-05-12]
cad/Sources/Grips/Slingshot Rifle Part-12.SLDPRT
21.4 x 32.0 x 100.0 mm
