CarloUser/Mobile-Mapping-Backpack/cad/Sources/Grips/Heavy-duty Slingshot Part-11.SLDPRT

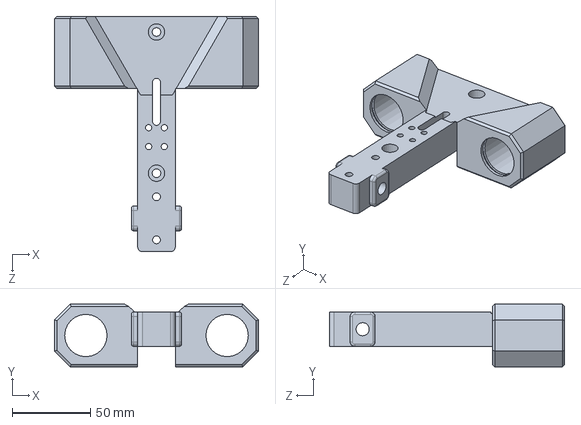
[picture p80: CAD file, 2026-05-12]
cad/Sources/Grips/Heavy-duty Slingshot Part-11.SLDPRT
130.0 x 40.0 x 150.0 mm
