CarloUser/Mobile-Mapping-Backpack/cad/Sources/Grips/Heavy-duty Slingshot Part-13.SLDPRT

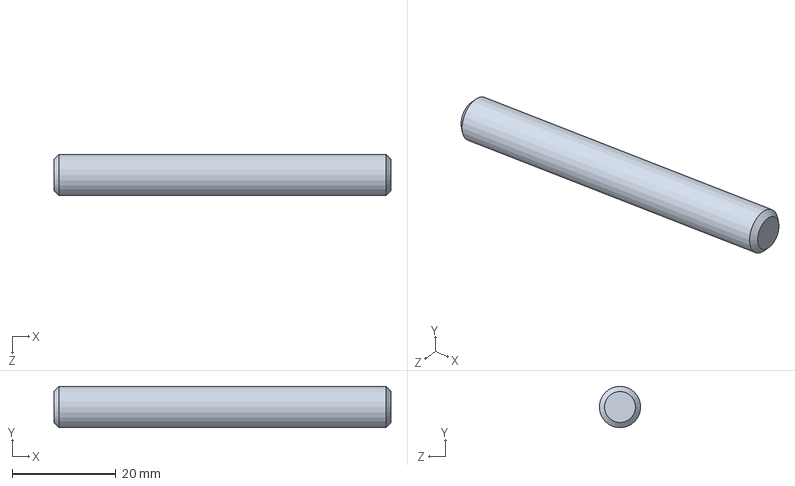
[picture p81: CAD file, 2026-05-12]
cad/Sources/Grips/Heavy-duty Slingshot Part-13.SLDPRT
65.0 x 8.00 x 8.00 mm
