CarloUser/Mobile-Mapping-Backpack/cad/Sources/Grips/LM16UU Libear Bearing.SLDPRT

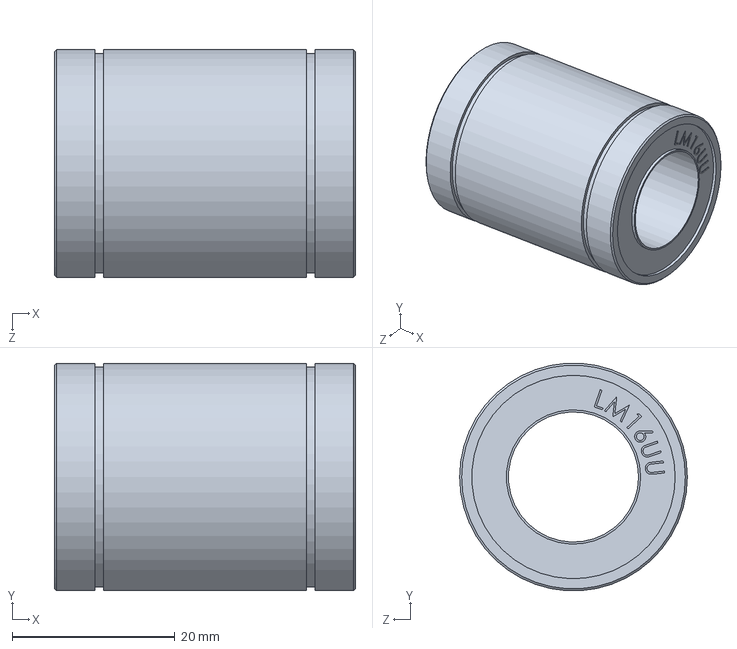
[picture p82: CAD file, 2026-05-12]
cad/Sources/Grips/LM16UU Libear Bearing.SLDPRT
37.0 x 27.9 x 28.0 mm
